EvGeniy0505/Electronic_Chess_Box/models/board/bottom.SLDPRT

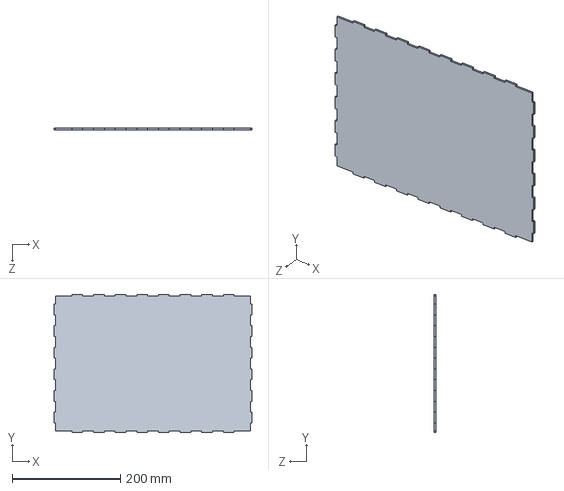
[picture p27: CAD file, 2025-05-28]
models/board/bottom.SLDPRT
366.0 x 256.0 x 3.00 mm
