EvGeniy0505/Electronic_Chess_Box/models/board/separator2.SLDPRT

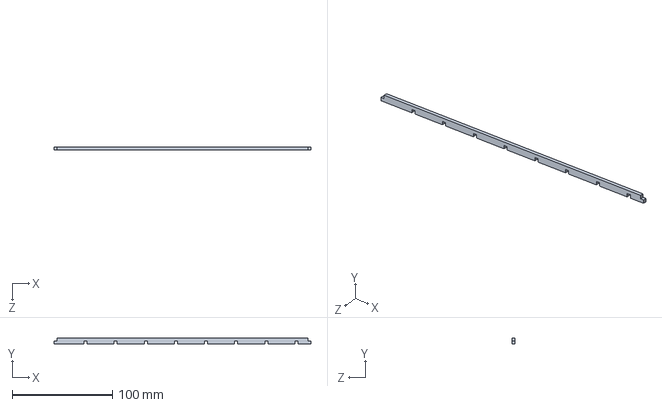
[picture p28: CAD file, 2025-05-28]
models/board/separator2.SLDPRT
256.0 x 6.00 x 3.00 mm
